mattaperkins/MIDIFresh/images/IMG_2144.jpeg

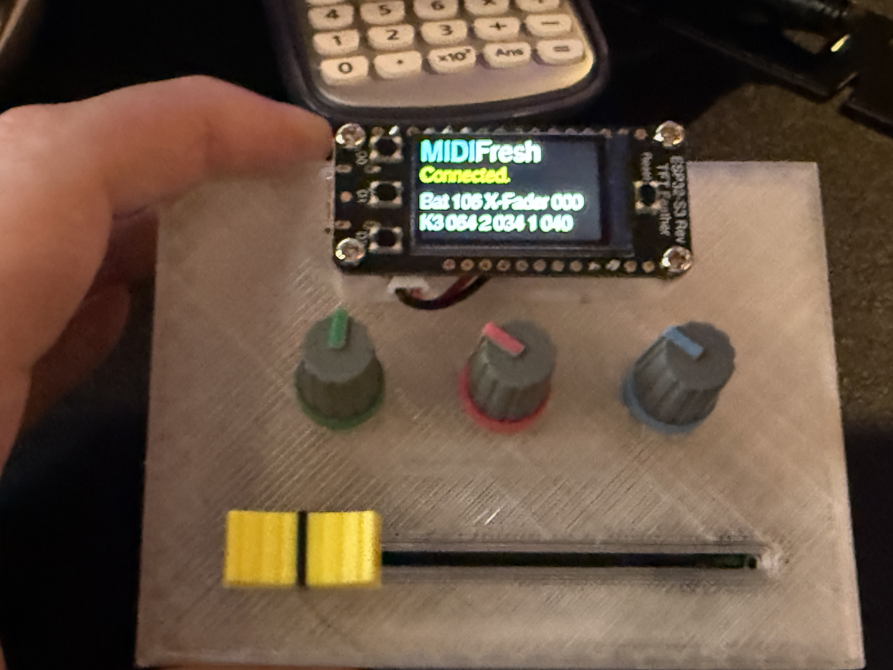
images/IMG_2144.jpeg
